w1024ji/nail_ArUco/marker.png

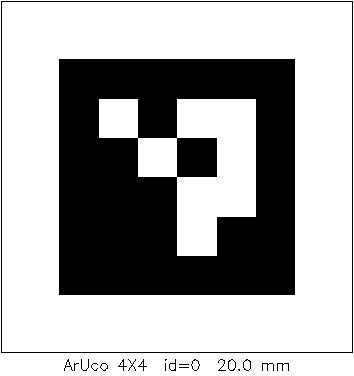
marker.png
