w1024ji/nail_ArUco/scan/out_live/all5.png

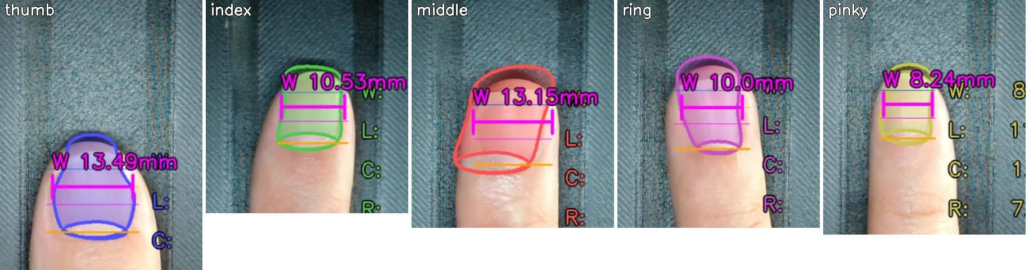
scan/out_live/all5.png
