w1024ji/nail_ArUco/scan/out_live/all5_v2.png

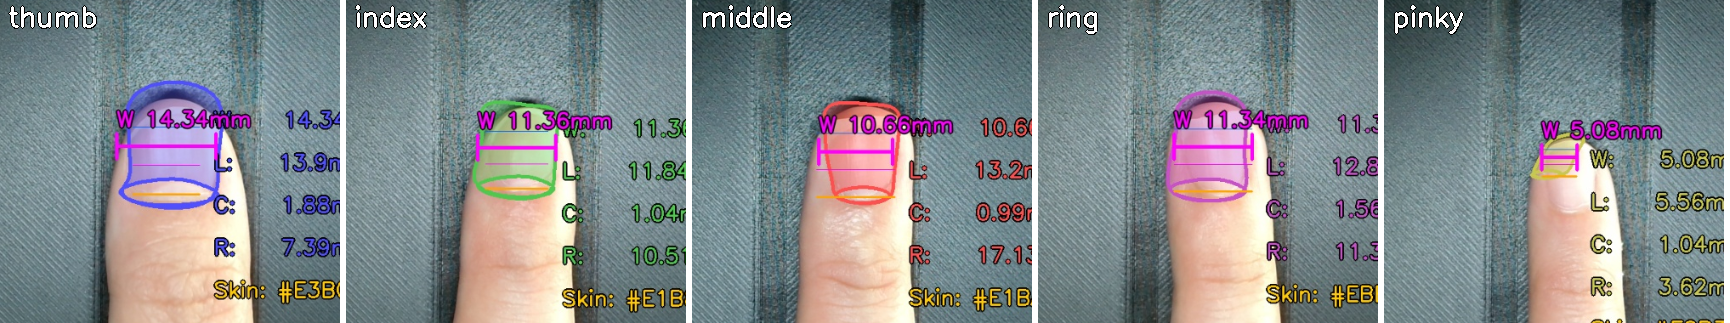
scan/out_live/all5_v2.png
