w1024ji/nail_ArUco/scan/out_live/index.jpg

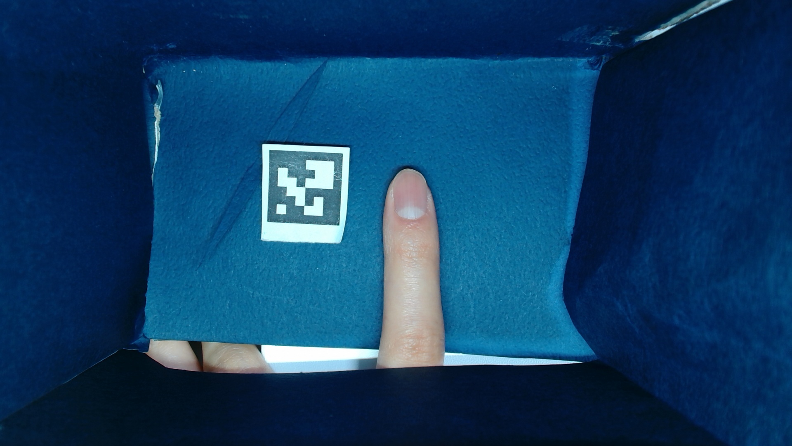
scan/out_live/index.jpg
