w1024ji/nail_ArUco/scan/out_live/index.png

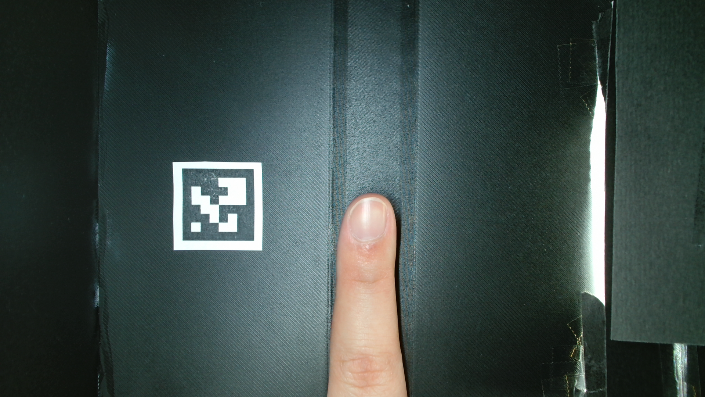
scan/out_live/index.png
