w1024ji/nail_ArUco/scan/out_live/nail_crop2.png

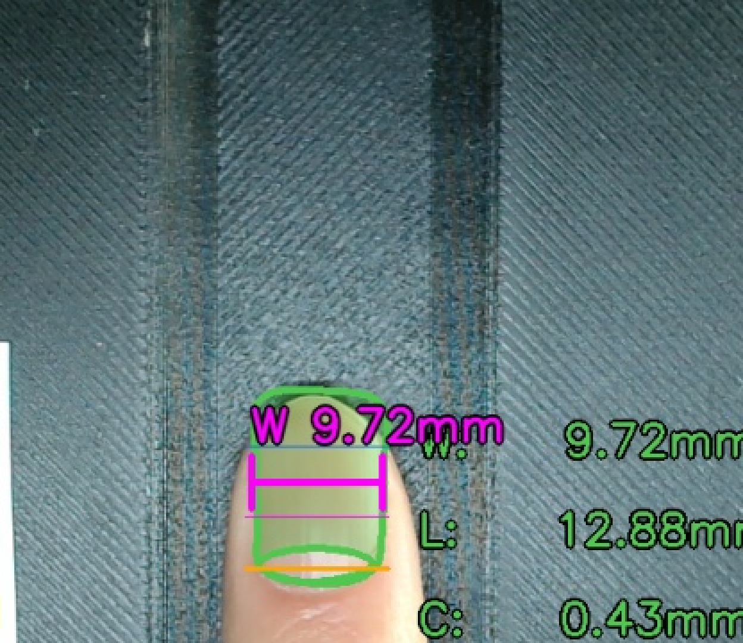
scan/out_live/nail_crop2.png
