w1024ji/nail_ArUco/scan/out_live/right_side.png

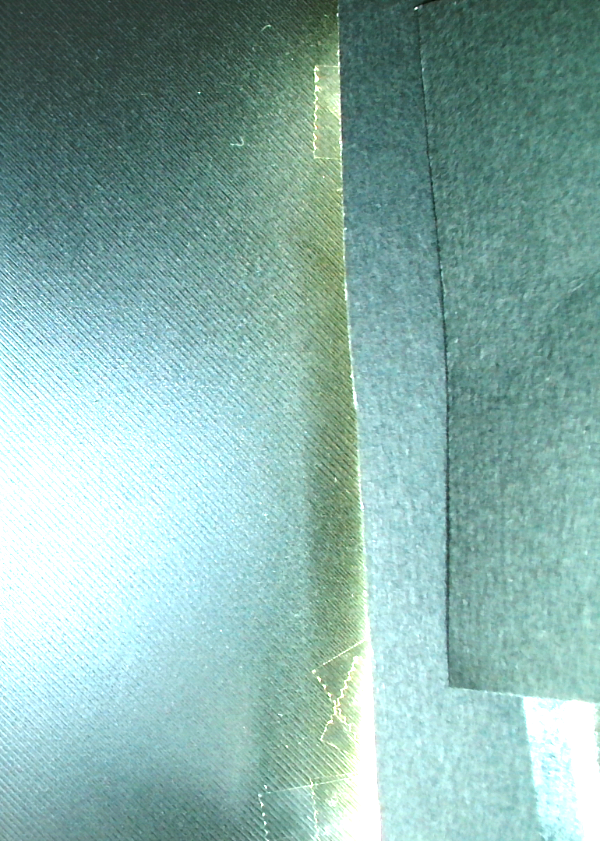
scan/out_live/right_side.png
