w1024ji/nail_ArUco/scan/out_live/thumb_crop.png

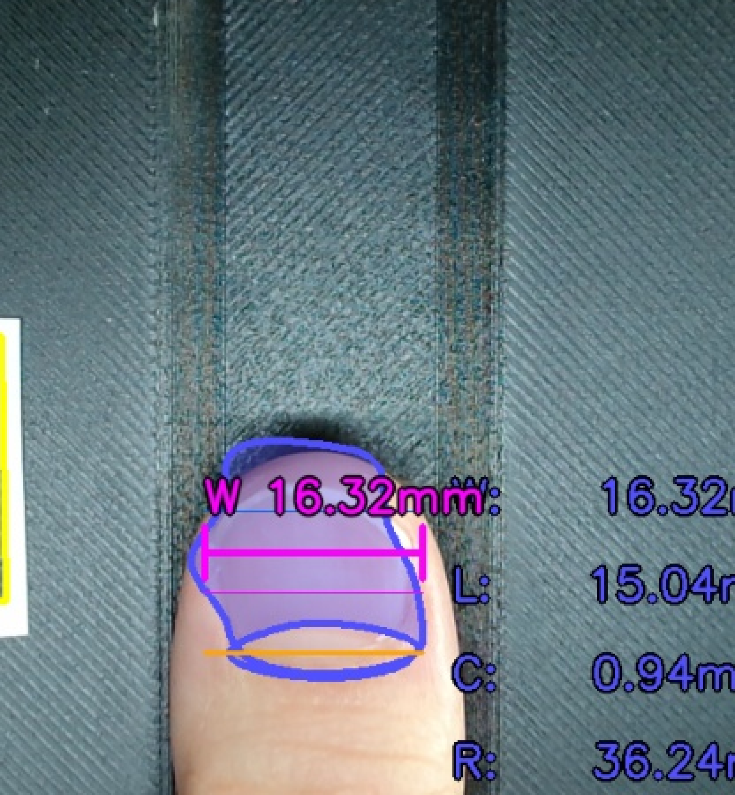
scan/out_live/thumb_crop.png
