w1024ji/nail_ArUco/scan/out_live/thumb_crop_left.png

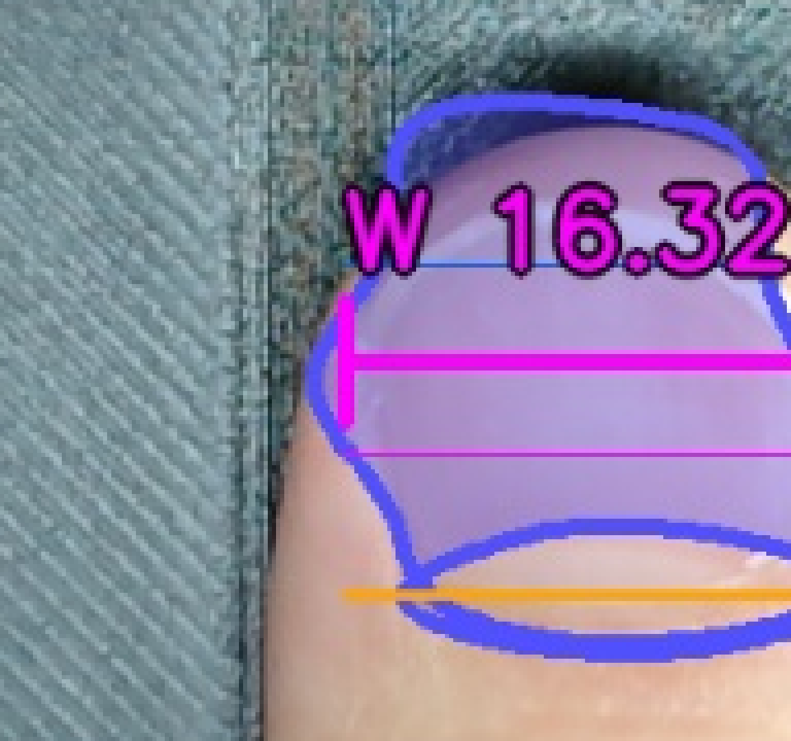
scan/out_live/thumb_crop_left.png
