w1024ji/nail_ArUco/scan/out_sh_middle_version2/middle_annotated.jpg

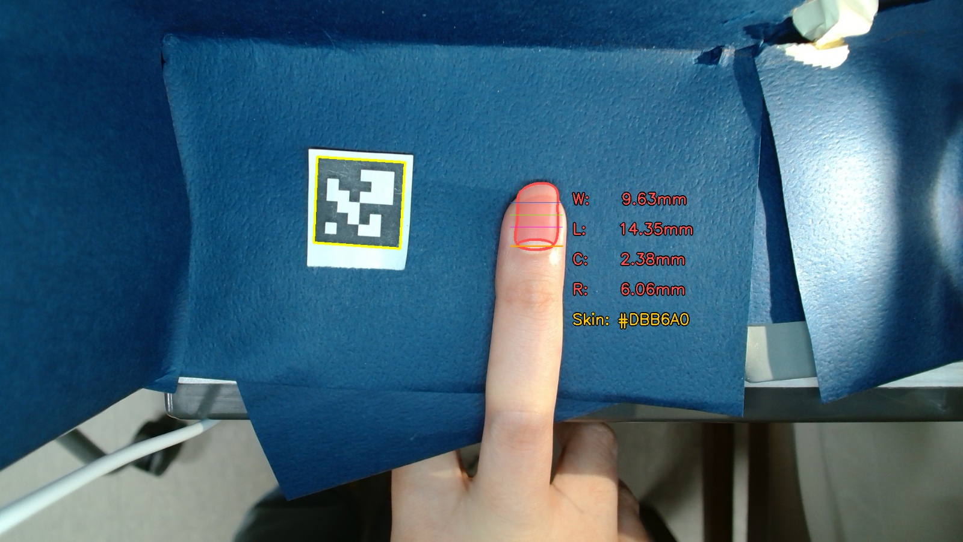
scan/out_sh_middle_version2/middle_annotated.jpg
