w1024ji/nail_ArUco/scan/out_sh_middle_version2/stl_preview.png

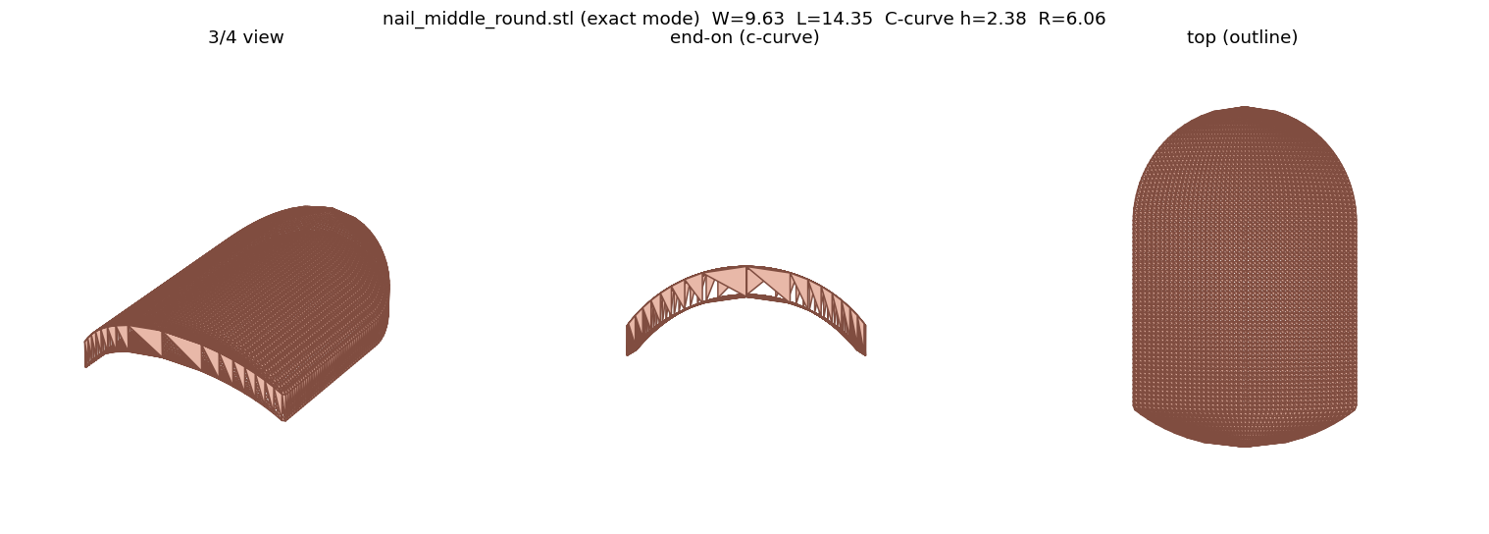
scan/out_sh_middle_version2/stl_preview.png
