w1024ji/nail_ArUco/scan/out_sh_thumb_version3/zoom.jpg

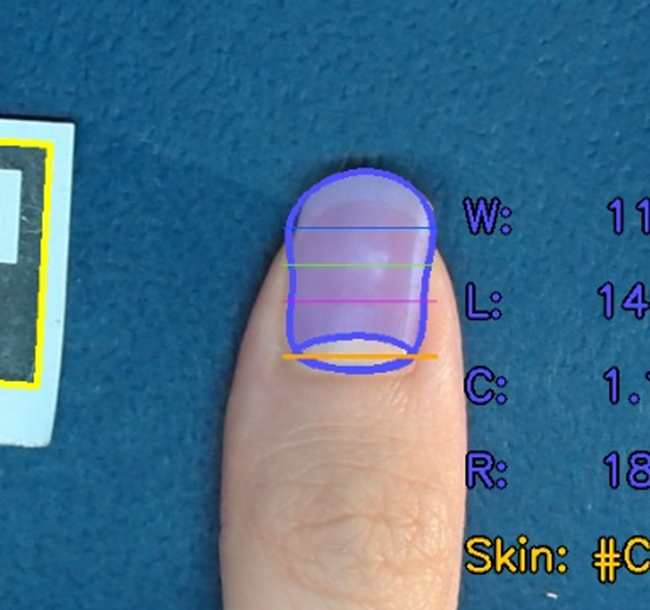
scan/out_sh_thumb_version3/zoom.jpg
