w1024ji/nail_ArUco/scan/out_ys_index/index_annotated.jpg

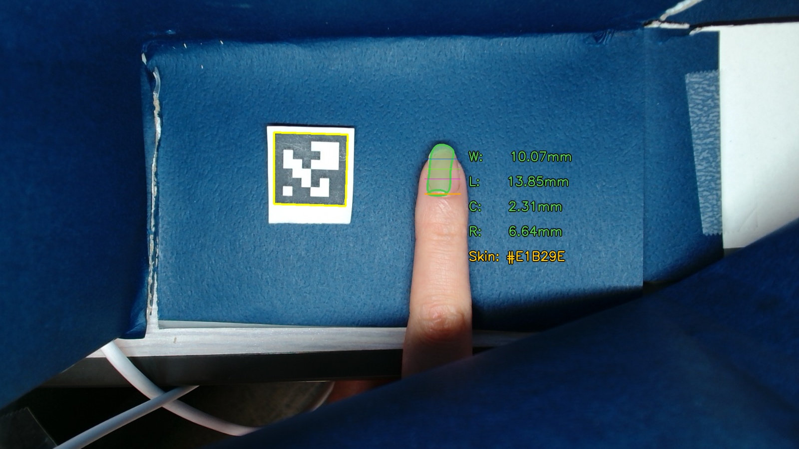
scan/out_ys_index/index_annotated.jpg
