w1024ji/nail_ArUco/scan/sh_images/sh_middle.jpg

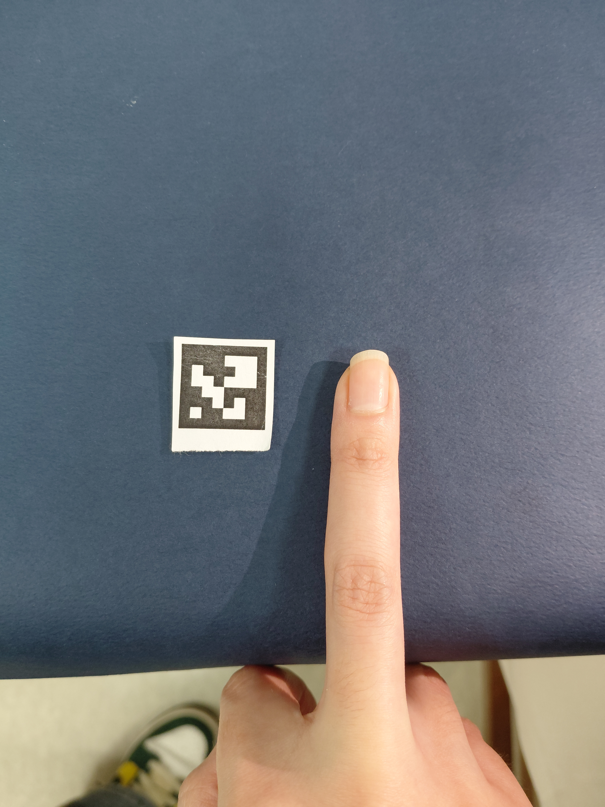
scan/sh_images/sh_middle.jpg
