w1024ji/nail_ArUco/scan/sh_images/sh_middle_ccurve.jpg

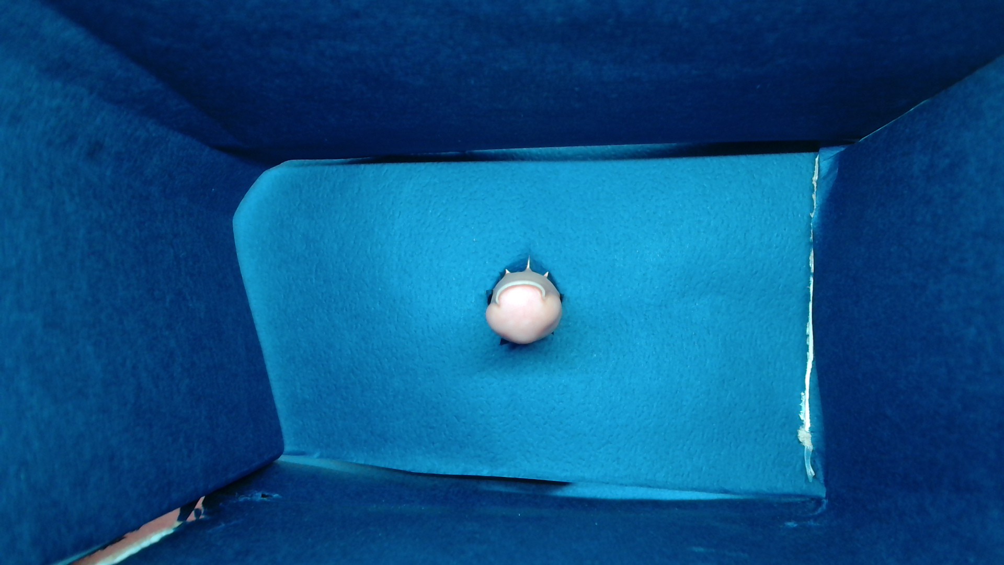
scan/sh_images/sh_middle_ccurve.jpg
