w1024ji/nail_ArUco/scan/sh_images/sh_thumb.jpg

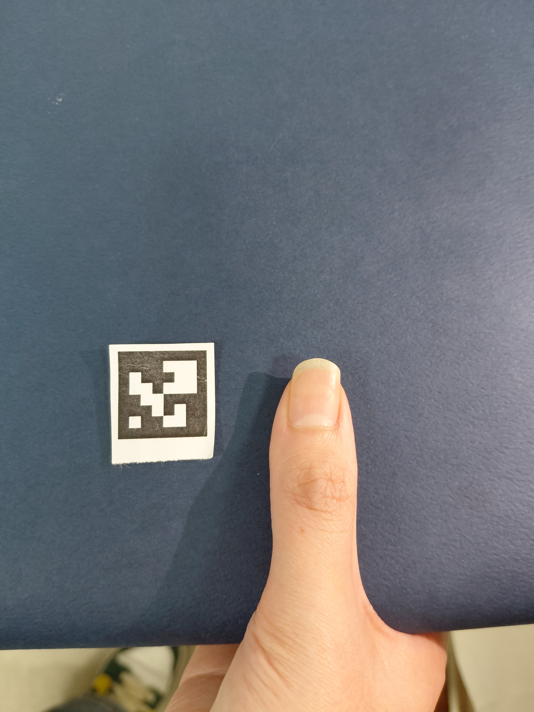
scan/sh_images/sh_thumb.jpg
