w1024ji/nail_ArUco/scan/sh_images/sh_thumb_version2.jpg

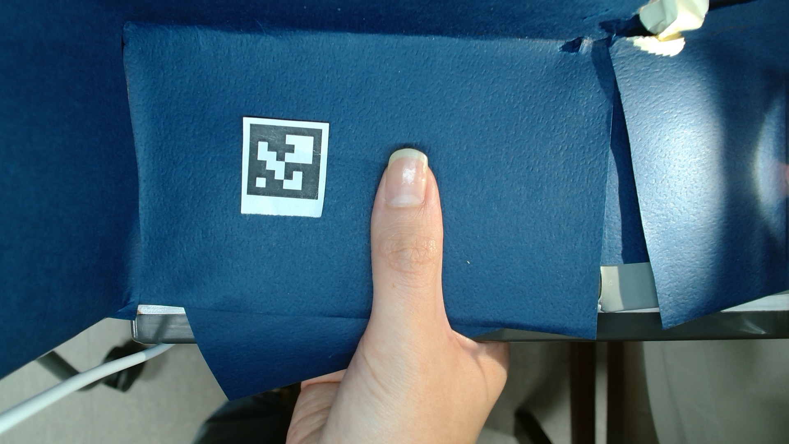
scan/sh_images/sh_thumb_version2.jpg
