w1024ji/nail_ArUco/scan/sh_images/sh_thumb_version3.jpg

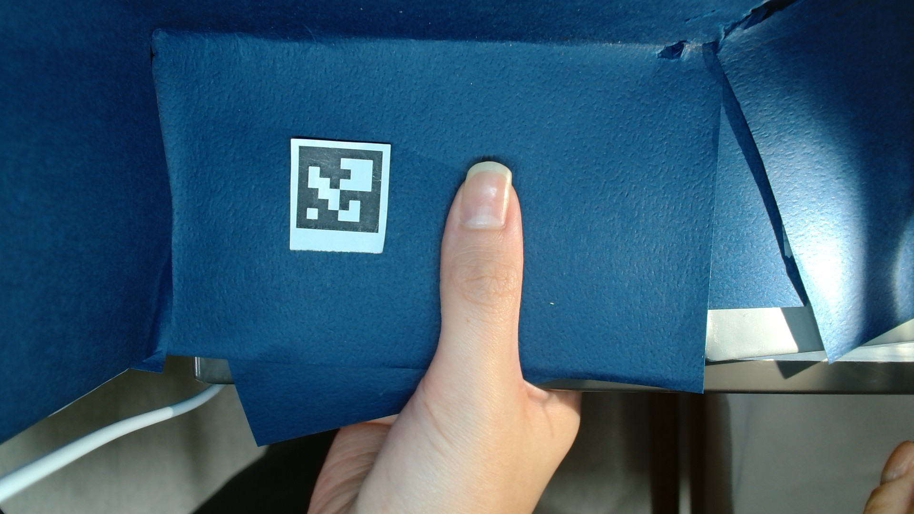
scan/sh_images/sh_thumb_version3.jpg
