w1024ji/nail_ArUco/scan/ys_images/ys_index_ccurve.jpg

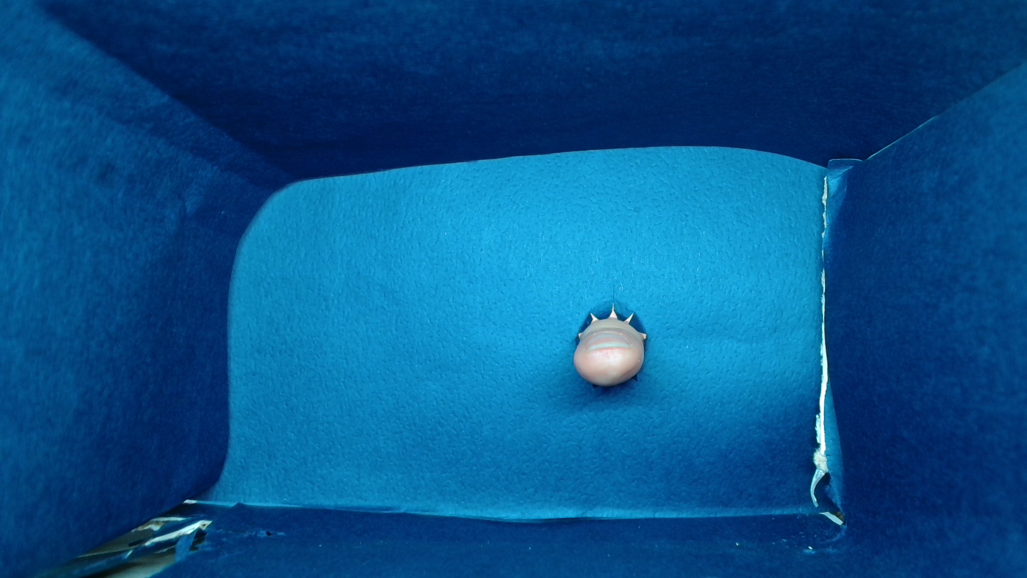
scan/ys_images/ys_index_ccurve.jpg
