w1024ji/nail_ArUco/results/index_annotated.jpg

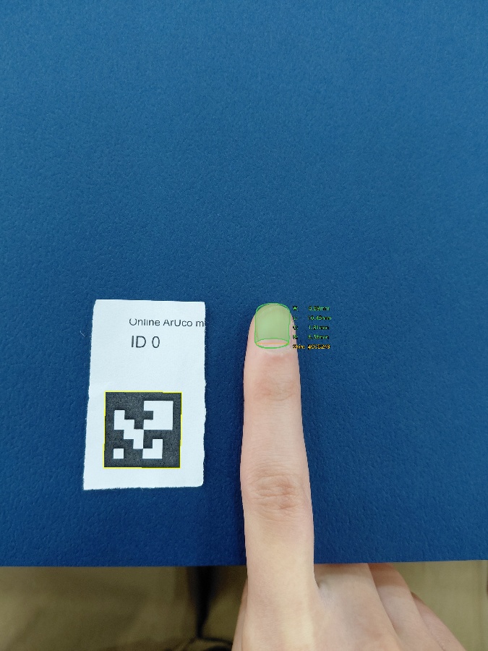
results/index_annotated.jpg
