w1024ji/nail_ArUco/scan/test/ccurve_band.png

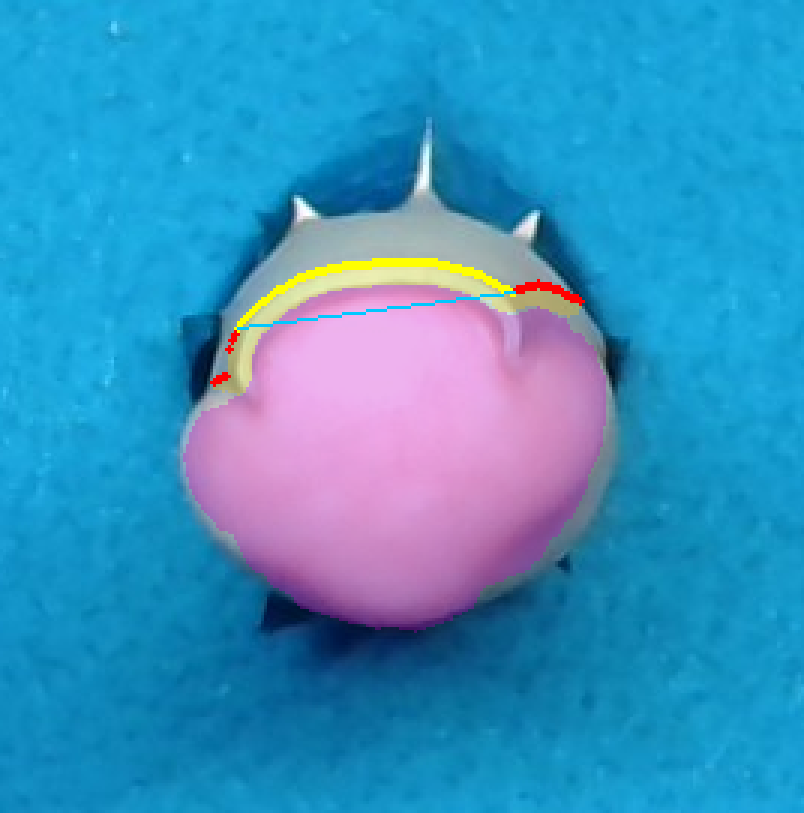
scan/test/ccurve_band.png
