w1024ji/nail_ArUco/scan/test/out_test_pinky_a/zoom.jpg

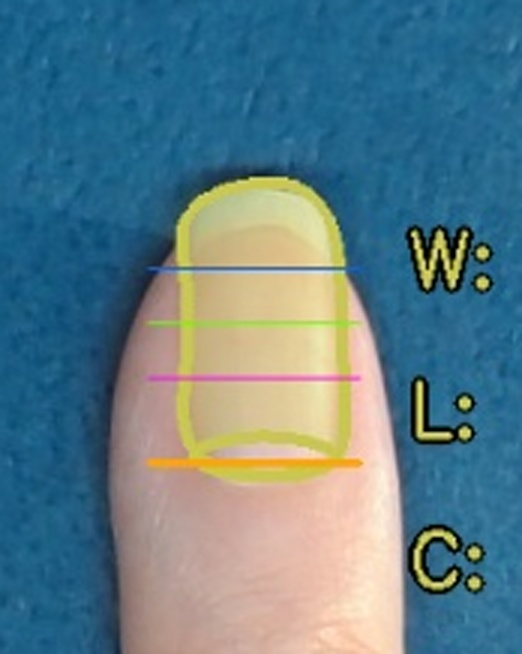
scan/test/out_test_pinky_a/zoom.jpg
