w1024ji/nail_ArUco/scan/test/out_test_ring_a/zoom.jpg

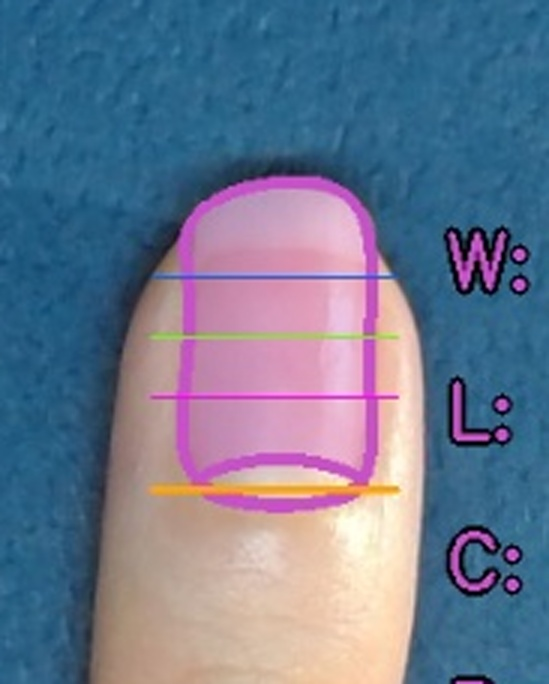
scan/test/out_test_ring_a/zoom.jpg
