w1024ji/nail_ArUco/scan/test/out_test_thumb_b/zoom.jpg

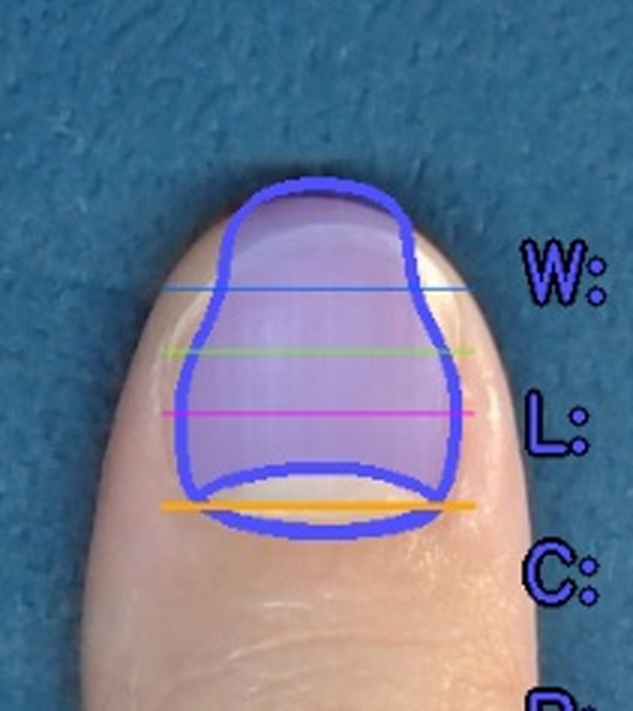
scan/test/out_test_thumb_b/zoom.jpg
