w1024ji/nail_ArUco/scan/test/test_index_b.jpg

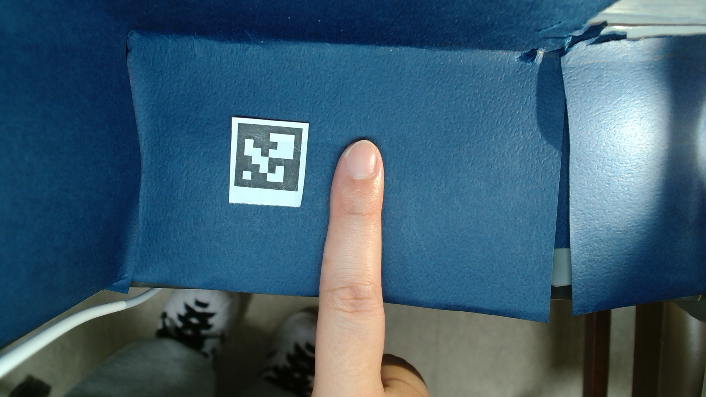
scan/test/test_index_b.jpg
