w1024ji/nail_ArUco/scan/out_ys_index/index_ccurve_debug.jpg

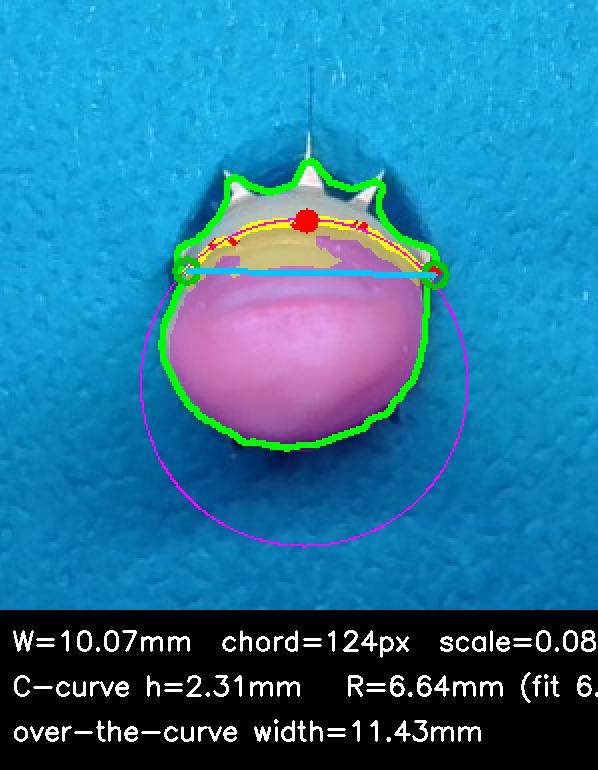
scan/out_ys_index/index_ccurve_debug.jpg
